bootuz-dinamon/ender3-v3-se-full-klipper/wled.cfg

[gcode_macro WLED_ON]
description: Turn WLED strip on using optional preset and resets led colors
gcode:
  {% set strip = params.STRIP|string %}
  {% set preset = params.PRESET|default(-1)|int %}

  {action_call_remote_method("set_wled_state",
                             strip=strip,
                             state=True,
                             preset=preset)}

[gcode_macro WLED_CONTROL]
description: Control effect values and brightness
gcode:
  {% set strip = params.STRIP|default('lights')|string %}
  {% set brightness = params.BRIGHTNESS|default(-1)|int %}
  {% set intensity = params.INTENSITY|default(-1)|int %}
  {% set speed = params.SPEED|default(-1)|int %}

  {action_call_remote_method("set_wled_state",
                             strip=strip,
                             brightness=brightness,
                             intensity=intensity,
                             speed=speed)}

[gcode_macro WLED_OFF]
description: Turn WLED strip off
gcode:
  {% set strip = params.STRIP|string %}

  {action_call_remote_method("set_wled_state",
                             strip=strip,
                             state=False)}

[gcode_macro SET_WLED]
description: SET_LED like functionality for WLED, applies to all active segments
gcode:
    {% set strip = params.STRIP|string %}
    {% set red = params.RED|default(0)|float %}
    {% set green = params.GREEN|default(0)|float %}
    {% set blue = params.BLUE|default(0)|float %}
    {% set white = params.WHITE|default(0)|float %}
    {% set index = params.INDEX|default(-1)|int %}
    {% set transmit = params.TRANSMIT|default(1)|int %}

    {action_call_remote_method("set_wled",
                               strip=strip,
                               red=red, green=green, blue=blue, white=white,
                               index=index, transmit=transmit)}
